2802691829/codex-usb-pager/docs/program-history/specs/2026-07-26-exact-blossom-60fps-design.md

# 精确 Blossom 花瓣与 50-60 FPS 屏显设计

## 最终验收标准

这次重构完成后，实物必须满足：

1. 单块花瓣就是用户图片中标出的那一整段闭合编织带，不是围绕 Logo
   镂空区域生成的近似图形。
2. 六块花瓣聚合后，必须逐像素还原原版 OpenAI Blossom，不能出现缝隙、
   凸起、双重边缘、粗细变化或大小跳变。
3. 就绪态的六块绿色花瓣比现在更分散，并围绕中心连续缓慢公转。
4. 运行态使用较深的紫色完整 Blossom，连续旋转。
5. 动画稳定帧率不得低于 50 FPS，优先达到 60 FPS。
6. 用户发出指令后，下一可用帧立即开始聚合；聚合过程中六瓣由绿色
   连续、动态地渐变成紫色，并在聚合完成时到达运行紫色。
7. 屏幕中央保留一个固定的白色正六边形线框；上下两个尖顶分别到达
   240×240 可视区的最上端和最下端。
8. 不得出现周期性停顿、从上到下的刷新波纹、方形虚影、蓝黑色带或花瓣裁边。

完整运行态 Blossom 的唯一来源仍为 `assets/openai-blossom.svg`。分散状态
单块花瓣的唯一来源改为用户最终确认的
`assets/reference-petal-exact.png`：生成器只截取其中的纯黑前景并按比例
缩放，不再从 SVG 镂空推导、平滑、补线或重新绘制。

## 花瓣必须怎样拆分

每一块花瓣都是原版 Blossom 中的一整段闭合编织带，包括：

- 外侧圆弧；
- 内侧折线；
- 与相邻编织带形成上下穿插关系的两端边界；
- 分离显示时平滑、闭合的完整轮廓。

生成程序直接读取用户最终确认的黑白花瓣图，阈值化后裁到前景边界；
这份遮罩就是标准花瓣，不再套用任何旧的轮廓推导。六块花瓣共享同一份
遮罩，通过独立的位置和角度变换显示，避免六份素材产生比例差异。

花瓣只允许在渲染时从同一份标准遮罩旋转，不允许在 128×128 遮罩上
连续旋转并回写，避免累计插值误差。

不能再使用“把六个镂空区域向外膨胀成环”的旧方法，也不能重新画一条
相似曲线。

生成结果必须遵守：

1. 标准花瓣必须逐像素等于参考图的纯黑前景。
2. 六块花瓣都使用相同遮罩、相同缩放，不能有单独缩小或拉伸。
3. 就绪态只做整体逆时针 90° 定向，不叠加旧方案的 180° 翻转。
4. 标准聚合位置不能出现尺寸跳变；聚合末段平滑切换到完整 SVG Blossom。
5. 不添加封口、圆角、平滑重画或拼接豁口。

生成程序同时输出每块花瓣的边界、中心、旋转安全裁剪范围和可选封口遮罩。
网页或图片预览与芯片固件必须使用同一份生成数据。

## 固定白色六边形框

- 使用尖顶的正六边形，中心与 240×240 屏幕可视区中心一致。
- 上顶点到达可视区最上端，下顶点到达可视区最下端。
- 因为正六边形比例限制，左右允许自然留白，不拉伸六边形。
- 线条为细白线，粗细恒定，边缘抗锯齿。
- 六边形是所有状态共用的固定框，不旋转、不缩放、不漂移。
- 白线亮度需要清晰可见，但不能比 Blossom 主体更抢眼。
- 花瓣、余额数字和状态动画都必须保留在六边形的安全视觉范围内。

## 各状态动画

### 就绪

- 六块花瓣为绿色。
- 六块花瓣均匀分布在中心周围。
- 分散轨道半径采用预览验证值约 68 像素，并允许为六边形安全边距做
  1 像素以内的最终取整。
- 只改变花瓣位置，不改变原版花瓣比例和大小。
- 每块花瓣以用户确认方案为基准整体逆时针旋转 90°。
- 任意公转角度下，花瓣与白色六边形至少保留 3 个实体屏幕像素的净距。
- 周余额数字显示在正中心。
- 六瓣以较慢速度连续公转，不能转一下停一下。

### 就绪切换到运行

- 收到用户指令后的第一帧立即开始向中心聚合。
- 六块精确花瓣沿平滑曲线向原版标准位置聚合，同时由绿色连续渐变成
  运行紫色。
- 颜色渐变与位置聚合使用同一条连续时间轴，不能先变色再聚合，也不能
  聚合完成后突然变色。
- 分散状态专用封口在聚合末段淡出。
- 聚合结束时，六瓣合并图必须与完整原版 Blossom 逐像素一致。
- 随后切换到单层完整 Blossom 渲染，切换前后画面不能有任何跳变。

### 运行

- 只渲染一个完整原版 Blossom 遮罩。
- 完成聚合后不再计算六个花瓣层。
- Blossom 持续旋转，不能周期性停顿。
- 紫色需要比当前更深、更饱和，在实体 ST7789 屏上能明显看出。

### 运行结束并返回就绪

- 完整 Blossom 平滑减速。
- 在画面完全相同的位置切换回六块精确花瓣。
- 六瓣向外分离并逐渐变成绿色。
- 不能在拆分瞬间出现缝隙、线宽变化或尺寸跳变。

### 离线

- 仍使用同一套精确六花瓣。
- 六瓣以不同方向和节奏不规则漂浮。
- 离线恢复就绪时，花瓣保持分离，只需移动到规则公转位置，不先聚合成
  完整 Logo。

## 为什么现在帧率低

现有程序的主要问题是：

1. 即使某块花瓣离当前像素很远，每个像素仍然检查六个花瓣采样器。
2. 动画过渡时还会额外采样完整 Blossom。
3. 每帧扫描两个完整缓存来寻找差异。
4. 屏幕 DMA 每行启动一次并阻塞等待，一帧最多启动约 172 次。
5. 当前写死为 25 毫秒一帧，理论上已经把帧率限制在 40 FPS。

因此卡顿主要来自渲染与传输架构，不是 RP2040 性能不足。

## 新渲染架构

### 静态背景缓存

背景、固定白色六边形框和其他不变内容只绘制一次，保存在基础场景缓存中。
每个新帧只恢复上一帧的脏矩形，不重新计算整张背景。

### 花瓣精灵路径

就绪、离线、聚合和分离状态，只在每块花瓣自己的旋转安全矩形内绘制。
六块花瓣覆盖不到的像素不采样，也不传给屏幕。

### 运行态快速路径

运行状态只采样一个完整 Blossom 遮罩，不初始化六个花瓣采样器。完整
Blossom 的实际边界就是本帧的脏区域。

### DMA 连续传输

- 多行像素合并成一个连续 DMA 批次，不再每行启动并等待一次。
- 每个矩形批次只设置一次 ST7789 写入窗口。
- 硬件允许时，DMA 传输当前批次的同时，CPU 准备下一批像素。
- RGB565 字节顺序和已经验证正确的屏幕初始化参数保持不变。
- 大型 DMA 缓冲区使用静态内存，不放在线程栈上。
- 构建时检查 SRAM 占用，并保留明确的栈空间余量。

## 帧率与调度

- 首选帧间隔：16 毫秒，约 60 FPS。
- 就绪态和运行态持续帧率最低要求：50 FPS。
- 状态变化发生时不等待原定时器，立即绘制下一帧。
- 角度、位置和缩放全部根据真实经过时间计算，不能按帧数累加。
- 即使偶尔出现一帧较慢，动画也不能因此整体变慢或停顿。
- 下一帧时间基于固定时间轴累加，不能从“上一帧执行结束时间”重新计算，
  否则会逐渐漂移。

固件调试模式分别记录：

1. 动画模型计算时间；
2. 像素渲染时间；
3. DMA 提交和等待时间；
4. 整帧总时间；
5. 错过 16 毫秒截止时间的次数。

发布固件可以关闭统计输出，但实机性能验收时必须开启。

## 自动测试

### 花瓣资源测试

- 标准花瓣逐像素等于参考 PNG 的黑色前景。
- 六块固件花瓣引用同一份标准遮罩，尺寸和比例完全一致。
- 所有支持角度和缩放下，花瓣都不能超出生成的裁剪范围。
- 就绪态任意公转角度下不越过白色六边形，并保留至少 3 像素净距。
- 聚合末段切换到完整 Blossom 时不出现可见的尺寸跳变。

### 动画测试

- 就绪分散半径必须大于当前 20 像素。
- 聚合结束时六瓣必须到达原版标准位置。
- 进入运行的第一帧必须已经开始从绿色向紫色变化。
- 聚合进行期间，颜色必须连续向运行紫色变化；聚合完成时必须达到运行
  紫色。
- 六瓣切换到完整 Blossom 时，画面像素不能变化。
- 反向分离必须从相同的完整 Blossom 图开始。

### 性能与驱动测试

- 运行态只初始化并采样完整 Blossom。
- 花瓣状态只触碰生成的脏区域。
- DMA 必须按多行批次传输，不能每一行都阻塞等待。
- 帧调度使用 16 毫秒目标，状态改变必须立即触发。
- 静态缓冲区总量必须低于 RP2040 SRAM 限制，并保留栈余量。

## 实机验收

1. 单块花瓣与用户红线标出的完整编织段一致。
2. 就绪状态六瓣明显分散，比例与原版完全一致。
3. 聚合后恢复原版 Blossom，没有缝、重边或粗细变化。
4. 固定白色正六边形线框清晰、居中、不变形，上下尖顶分别到达屏幕
   可视区最上端和最下端。
5. 就绪和运行状态实测持续帧率不低于 50 FPS。
6. 运行旋转连续，没有周期性停顿。
7. 不出现逐行刷新波纹、方形虚影、蓝黑带或花瓣裁边。
8. 用户发出指令后，屏幕在下一可用帧同时开始聚合和由绿向紫渐变。

## 本次不改

- 已确认的屏幕 GPIO 8-12 接线。
- 板载灯“运行红色、停止白色”的行为。
- 蜂鸣器现有触发逻辑。
- 不通过加快动画速度来掩盖掉帧。
