2802691829/codex-usb-pager/enclosure/outputs/review-four-latch-cutaway.png

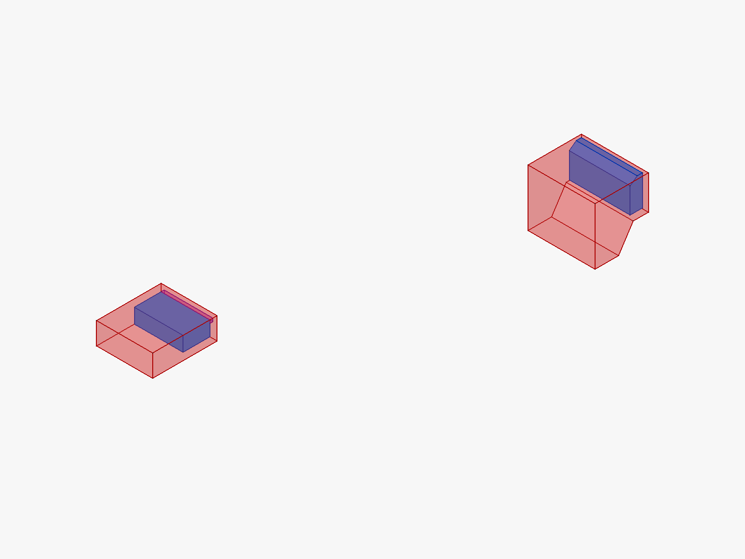
enclosure/outputs/review-four-latch-cutaway.png
