2802691829/codex-usb-pager/enclosure/outputs/review-front-exterior.png

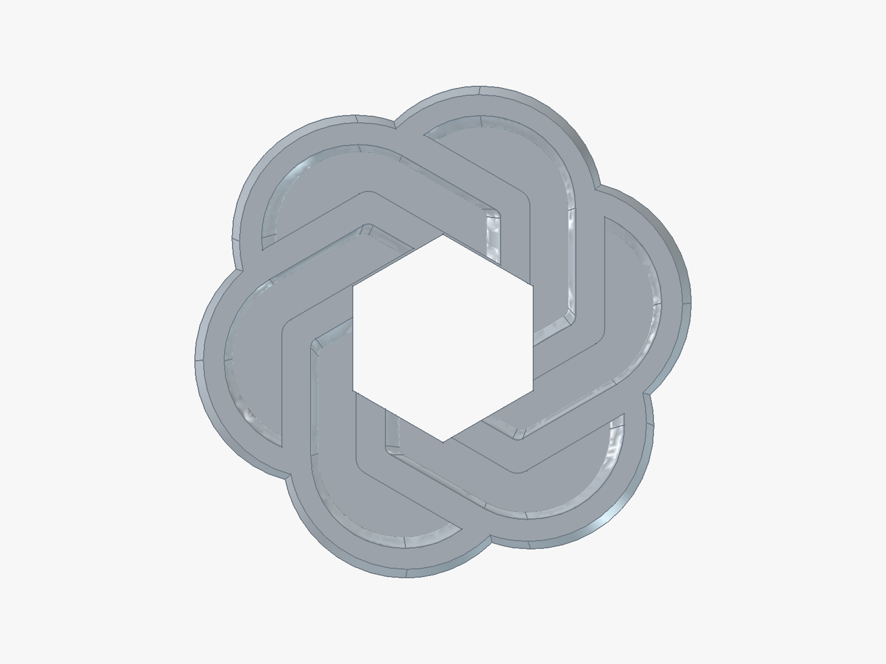
enclosure/outputs/review-front-exterior.png
