2802691829/codex-usb-pager/enclosure/outputs/review-front-inside.png

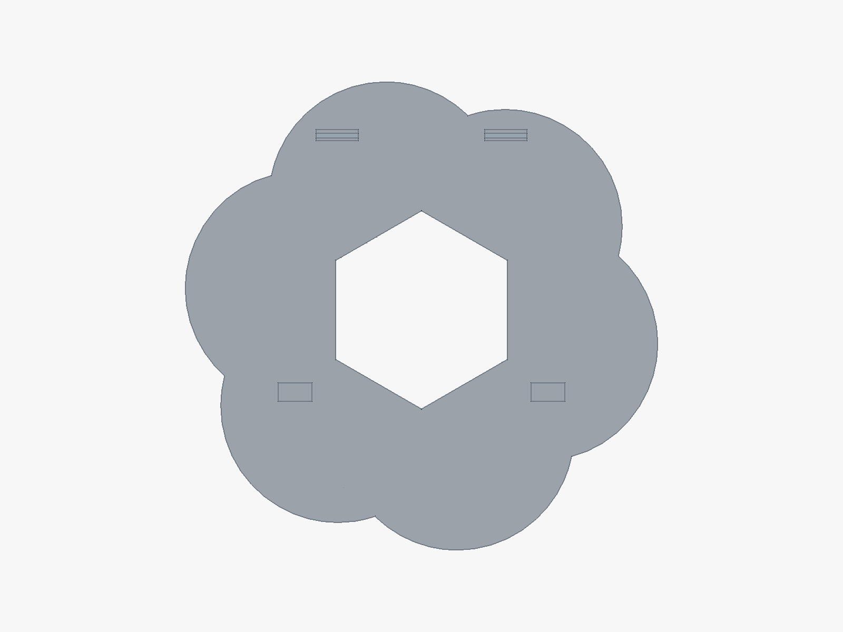
enclosure/outputs/review-front-inside.png
