2802691829/codex-usb-pager/enclosure/outputs/review-rear-exterior.png

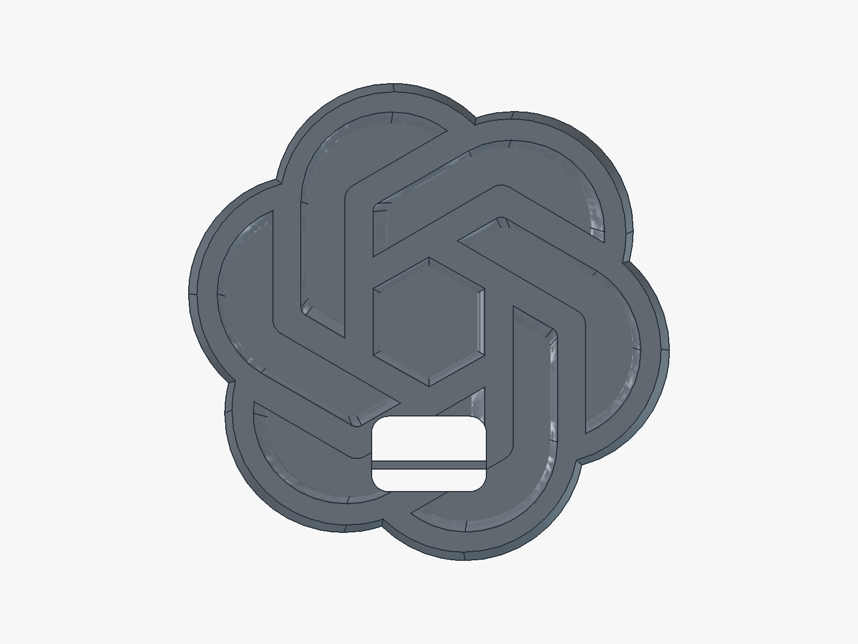
enclosure/outputs/review-rear-exterior.png
