2802691829/codex-usb-pager/enclosure/outputs/review-screen-setback-section.png

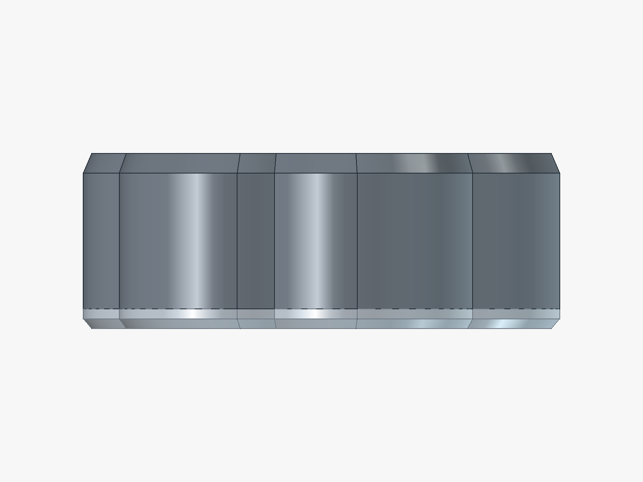
enclosure/outputs/review-screen-setback-section.png
