2802691829/codex-usb-pager/enclosure/outputs/review-usb-shift.png

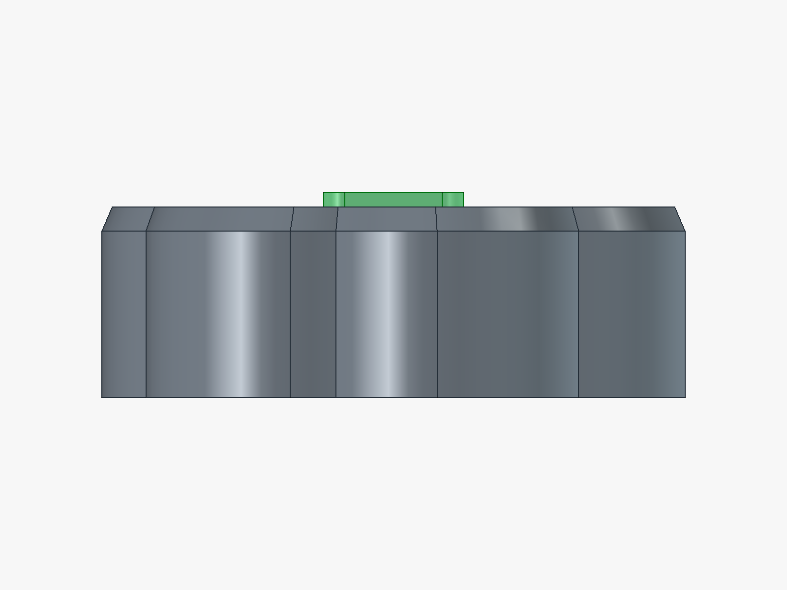
enclosure/outputs/review-usb-shift.png
