2802691829/codex-usb-pager/enclosure/outputs/review-assembly-1-tilted.png

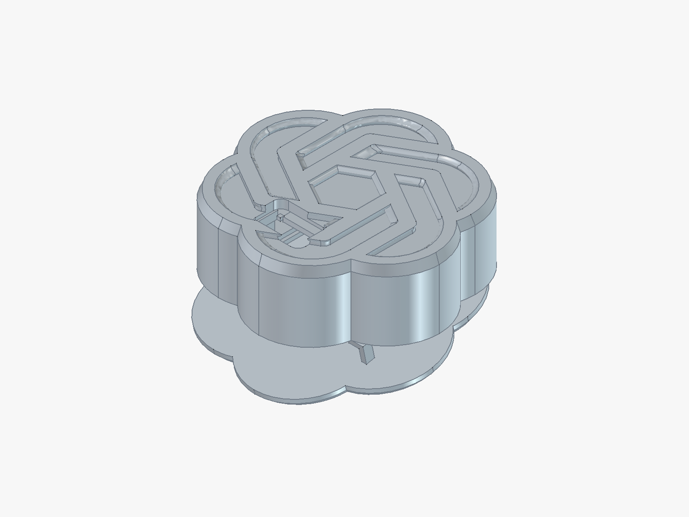
enclosure/outputs/review-assembly-1-tilted.png
