2802691829/codex-usb-pager/ports/rp2040-zero/firmware/include/display_pattern.h

#ifndef CODEX_DISPLAY_PATTERN_H
#define CODEX_DISPLAY_PATTERN_H

#include <stdint.h>

uint16_t pager_rgb565(uint8_t red, uint8_t green, uint8_t blue);
uint16_t pager_display_test_color(uint16_t x, uint16_t y);

#endif
