2802691829/codex-usb-pager/ports/rp2040-zero/firmware/src/st7789_profile.c

#include "st7789_profile.h"

const st7789_init_step_t g_st7789_vendor_init[] = {
    {0x36U, 1U, {0x00U}},
    {0x3AU, 1U, {0x05U}},
    {0xB2U, 5U, {0x0CU, 0x0CU, 0x00U, 0x33U, 0x33U}},
    {0xB7U, 1U, {0x35U}},
    {0xBBU, 1U, {0x19U}},
    {0xC0U, 1U, {0x2CU}},
    {0xC2U, 1U, {0x01U}},
    {0xC3U, 1U, {0x12U}},
    {0xC4U, 1U, {0x20U}},
    {0xC6U, 1U, {0x0FU}},
    {0xD0U, 2U, {0xA4U, 0xA1U}},
    {0xE0U,
     14U,
     {0xD0U, 0x04U, 0x0DU, 0x11U, 0x13U, 0x2BU, 0x3FU,
      0x54U, 0x4CU, 0x18U, 0x0DU, 0x0BU, 0x1FU, 0x23U}},
    {0xE1U,
     14U,
     {0xD0U, 0x04U, 0x0CU, 0x11U, 0x13U, 0x2CU, 0x3FU,
      0x44U, 0x51U, 0x2FU, 0x1FU, 0x1FU, 0x20U, 0x23U}},
    {0x21U, 0U, {0U}},
    {0x11U, 0U, {0U}},
    {0x29U, 0U, {0U}},
};

const size_t g_st7789_vendor_init_count =
    sizeof(g_st7789_vendor_init) / sizeof(g_st7789_vendor_init[0]);
