2802691829/codex-usb-pager/ports/rp2040-zero/firmware/src/tiny_font.c

#include "tiny_font.h"

#include <stddef.h>

typedef struct {
    char glyph;
    uint8_t rows[TINY_FONT_HEIGHT];
} tiny_glyph_t;

static const tiny_glyph_t glyphs[] = {
    {'0', {0x0EU, 0x11U, 0x13U, 0x15U, 0x19U, 0x11U, 0x0EU}},
    {'1', {0x04U, 0x0CU, 0x04U, 0x04U, 0x04U, 0x04U, 0x0EU}},
    {'2', {0x0EU, 0x11U, 0x01U, 0x02U, 0x04U, 0x08U, 0x1FU}},
    {'3', {0x1EU, 0x01U, 0x01U, 0x0EU, 0x01U, 0x01U, 0x1EU}},
    {'4', {0x02U, 0x06U, 0x0AU, 0x12U, 0x1FU, 0x02U, 0x02U}},
    {'5', {0x1FU, 0x10U, 0x10U, 0x1EU, 0x01U, 0x01U, 0x1EU}},
    {'6', {0x06U, 0x08U, 0x10U, 0x1EU, 0x11U, 0x11U, 0x0EU}},
    {'7', {0x1FU, 0x01U, 0x02U, 0x04U, 0x08U, 0x08U, 0x08U}},
    {'8', {0x0EU, 0x11U, 0x11U, 0x0EU, 0x11U, 0x11U, 0x0EU}},
    {'9', {0x0EU, 0x11U, 0x11U, 0x0FU, 0x01U, 0x02U, 0x0CU}},
    {'E', {0x1FU, 0x10U, 0x10U, 0x1EU, 0x10U, 0x10U, 0x1FU}},
    {'K', {0x11U, 0x12U, 0x14U, 0x18U, 0x14U, 0x12U, 0x11U}},
    {'W', {0x11U, 0x11U, 0x11U, 0x15U, 0x15U, 0x1BU, 0x11U}},
    {'%', {0x19U, 0x1AU, 0x02U, 0x04U, 0x08U, 0x0BU, 0x13U}},
};

bool tiny_font_sample(char glyph, uint8_t x, uint8_t y) {
    size_t index;

    if (x >= TINY_FONT_WIDTH || y >= TINY_FONT_HEIGHT) {
        return false;
    }
    for (index = 0U; index < sizeof(glyphs) / sizeof(glyphs[0]); ++index) {
        if (glyphs[index].glyph == glyph) {
            return (glyphs[index].rows[y] &
                    (uint8_t)(1U << (TINY_FONT_WIDTH - 1U - x))) != 0U;
        }
    }
    return false;
}
